abferguson/Camping-data-logger/CAD/exploded view.png

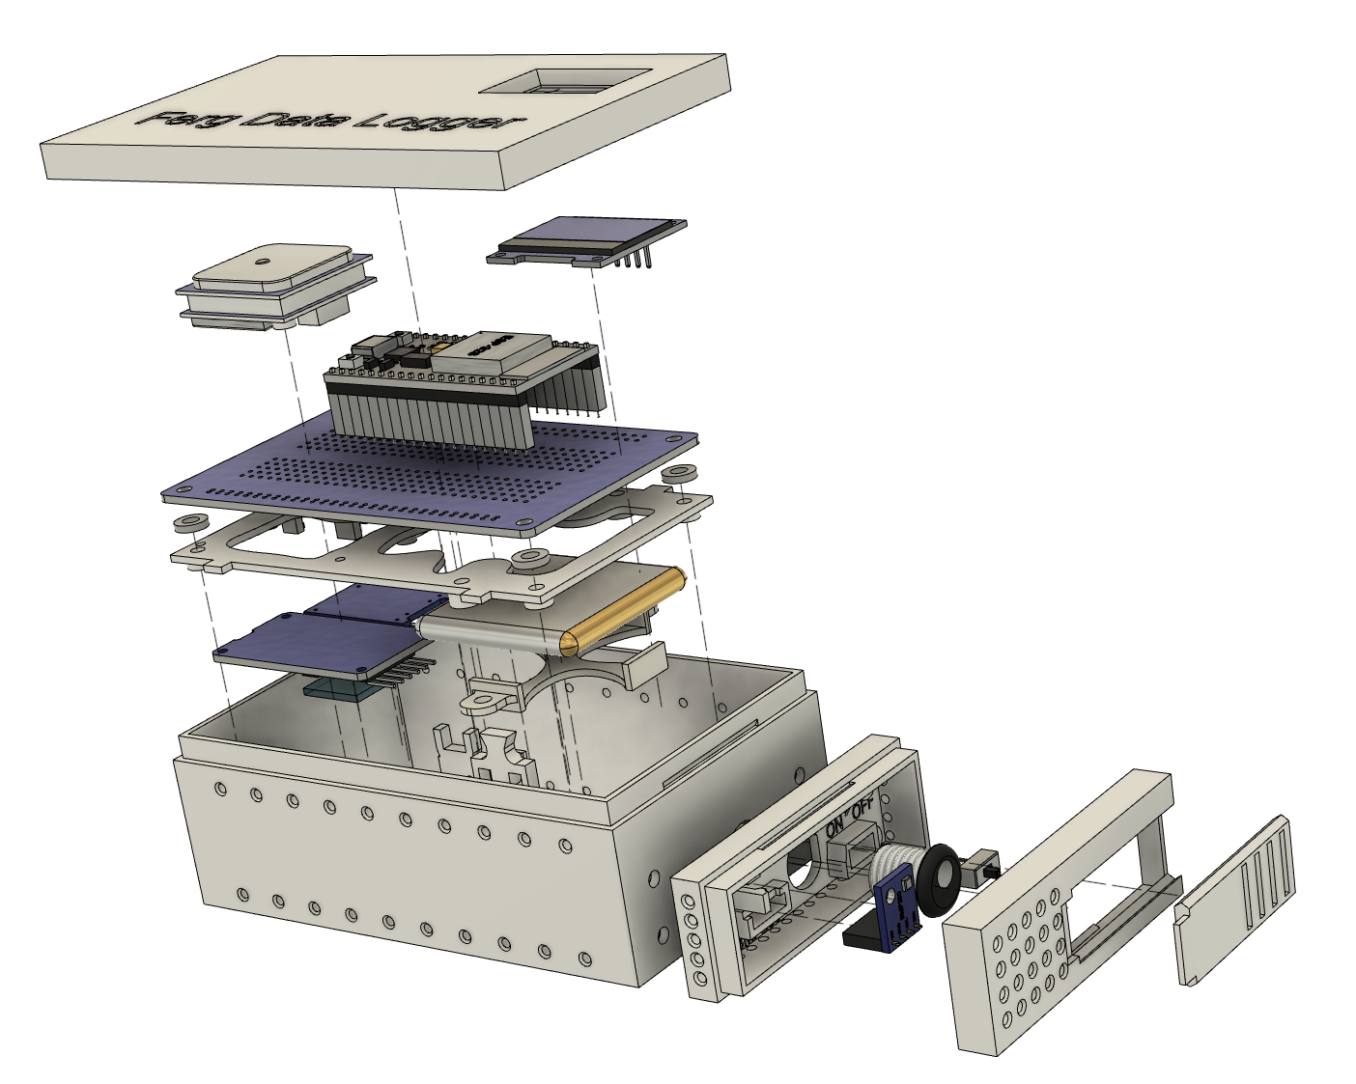
CAD/exploded view.png
