abferguson/Camping-data-logger/Circuit/data logger circuit.JPG

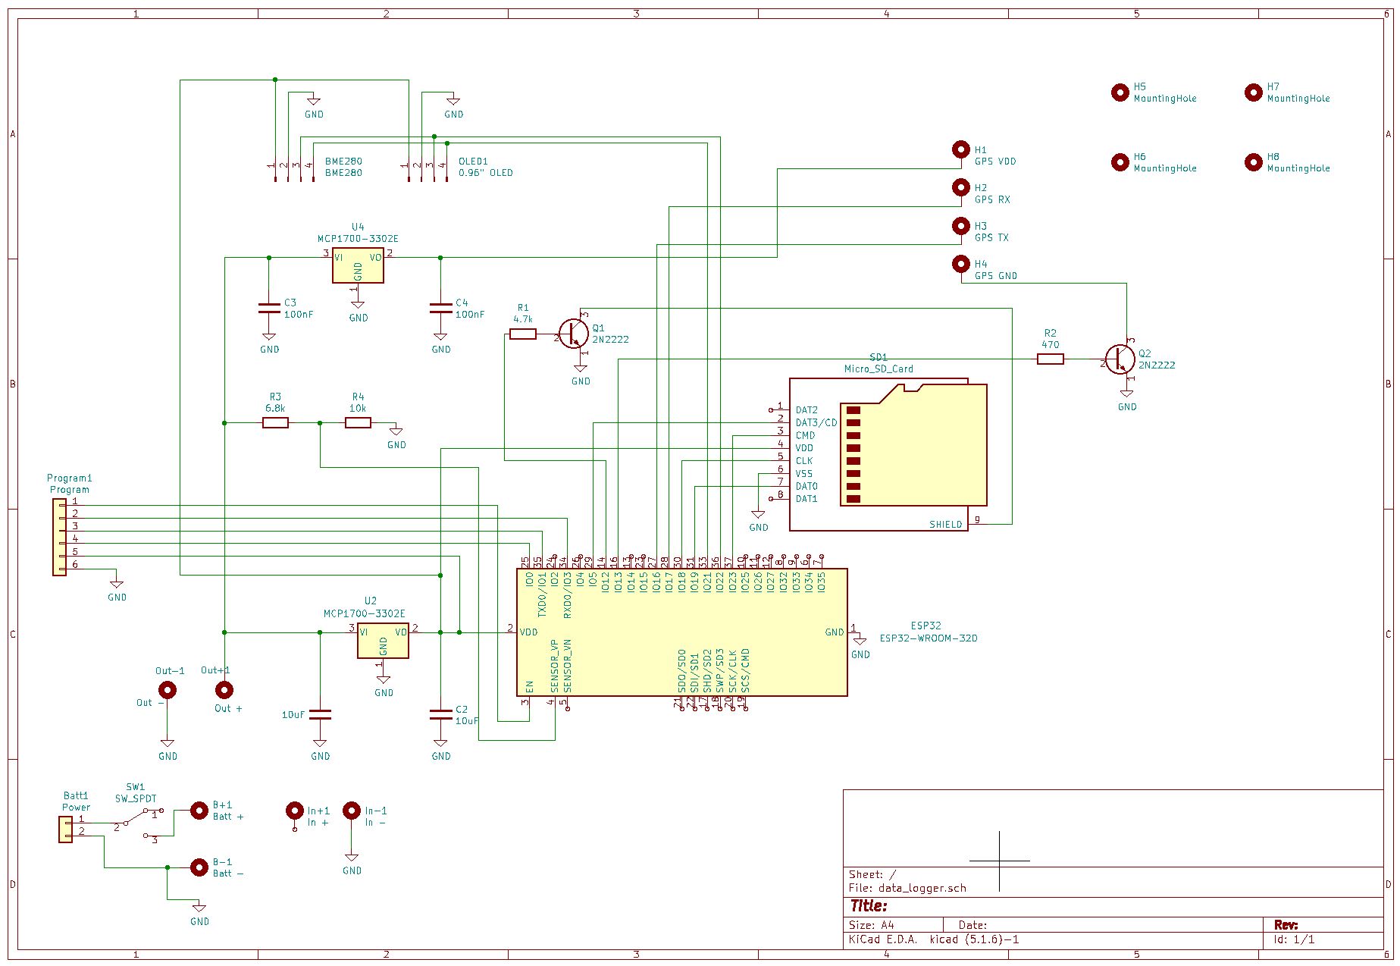
Circuit/data logger circuit.JPG
