abferguson/Camping-data-logger/Circuit/v11_circuit.JPG

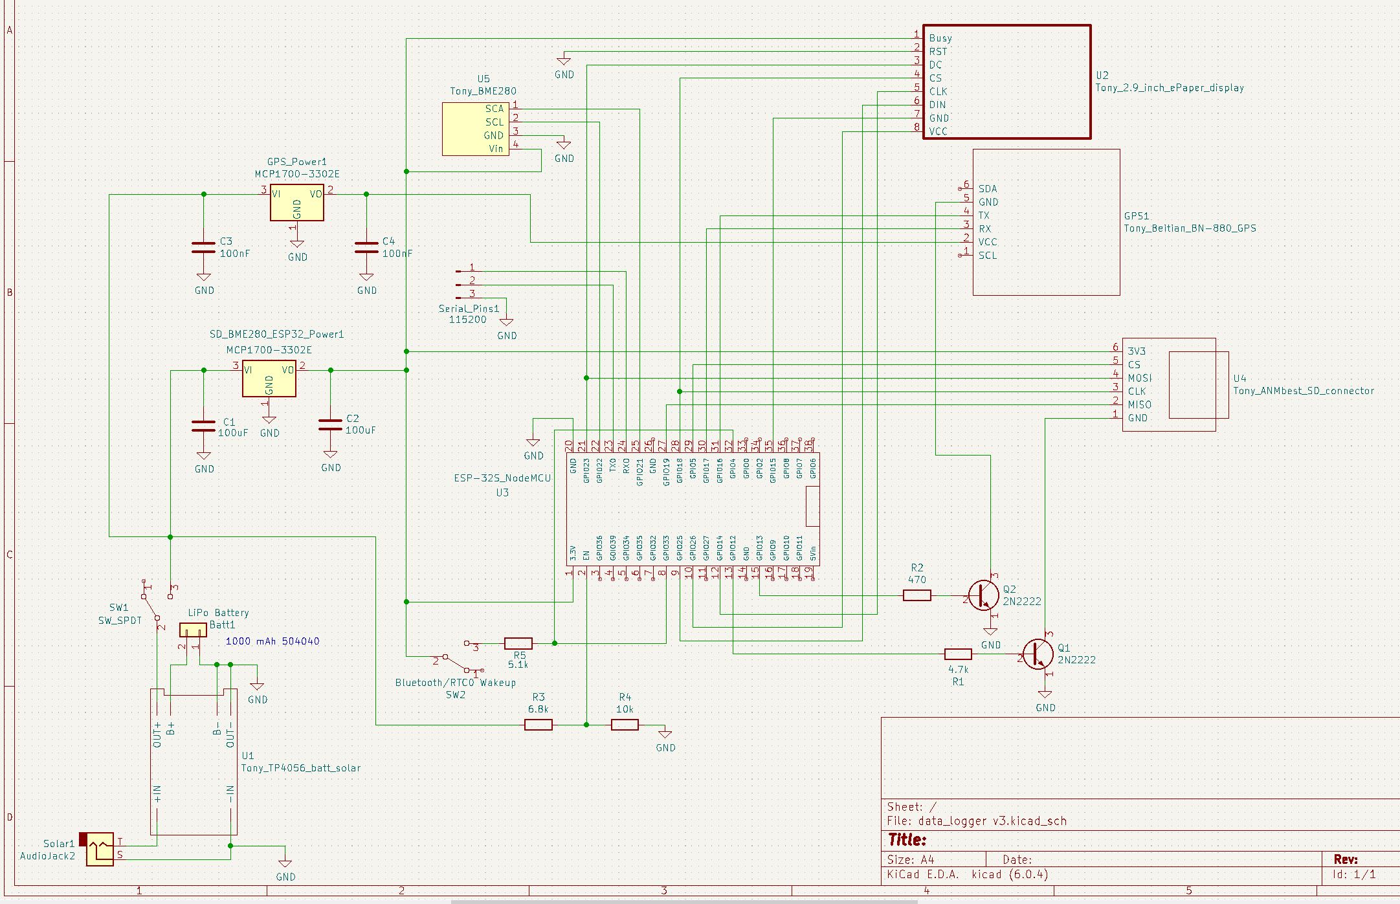
Circuit/v11_circuit.JPG
