abferguson/Camping-data-logger/Images/ABF_3092.jpg

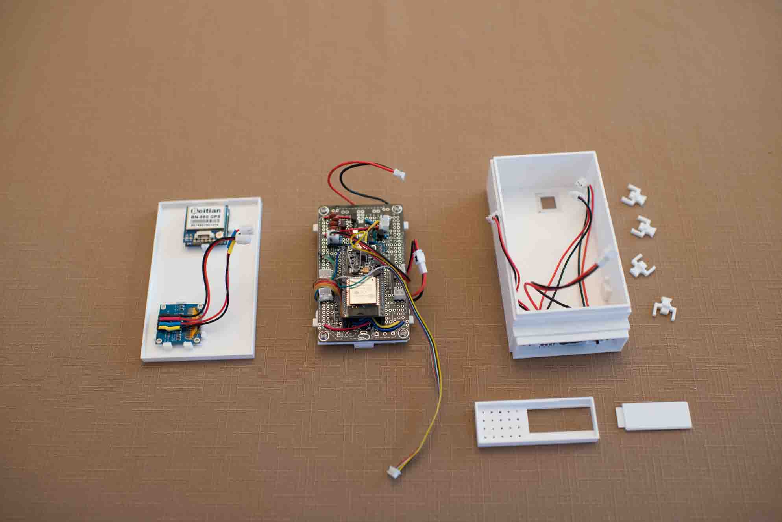
Images/ABF_3092.jpg
