abferguson/Camping-data-logger/Images/ABF_3096.jpg

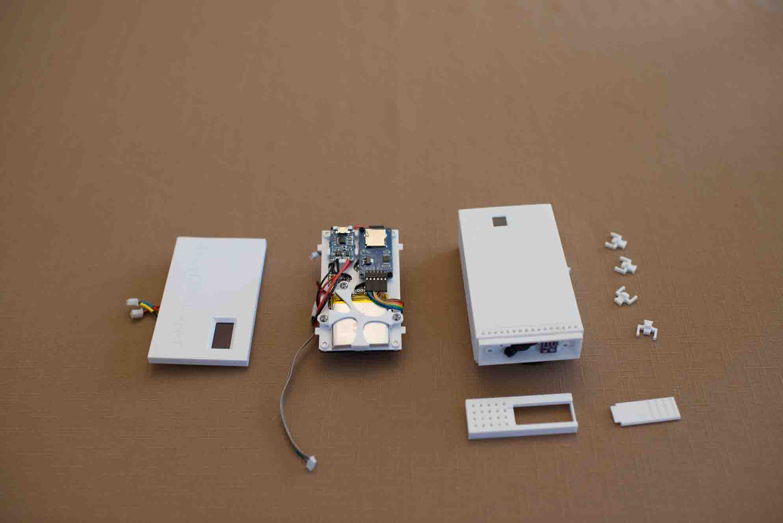
Images/ABF_3096.jpg
