abferguson/Camping-data-logger/Images/ABF_3097.jpg

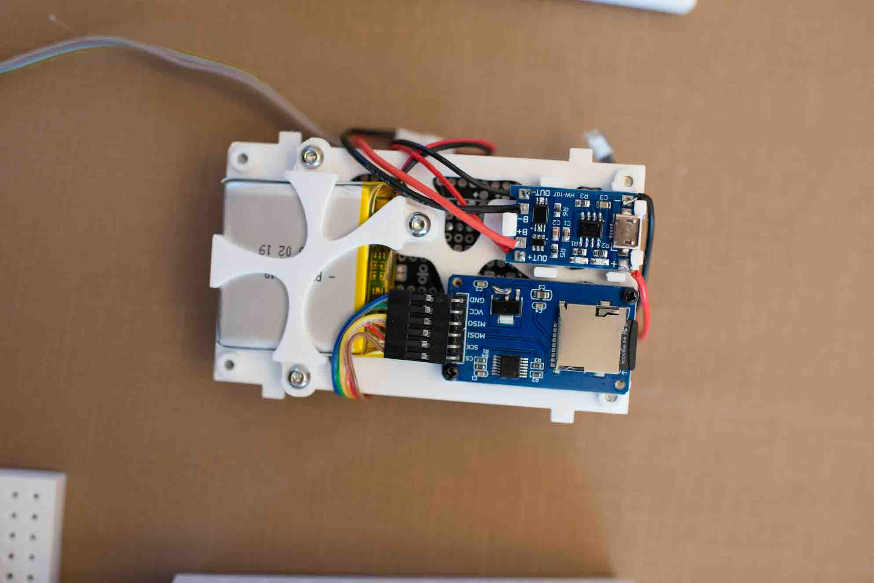
Images/ABF_3097.jpg
