abferguson/Camping-data-logger/Images/ABF_3098.jpg

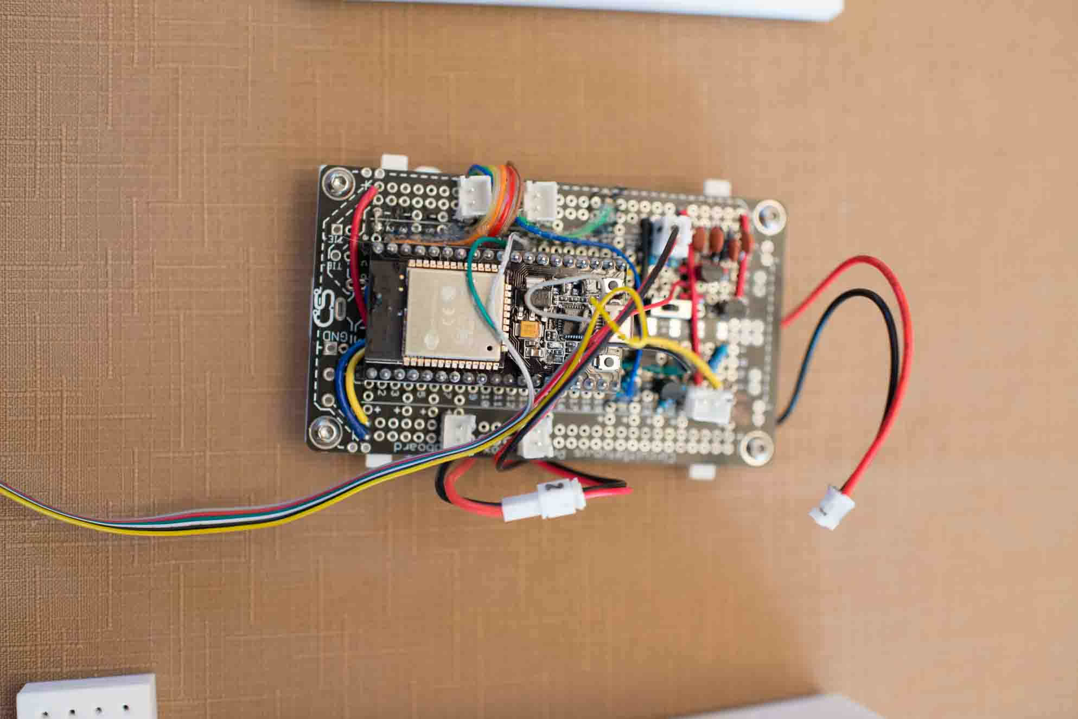
Images/ABF_3098.jpg
