abferguson/Camping-data-logger/Images/ABF_3099.jpg

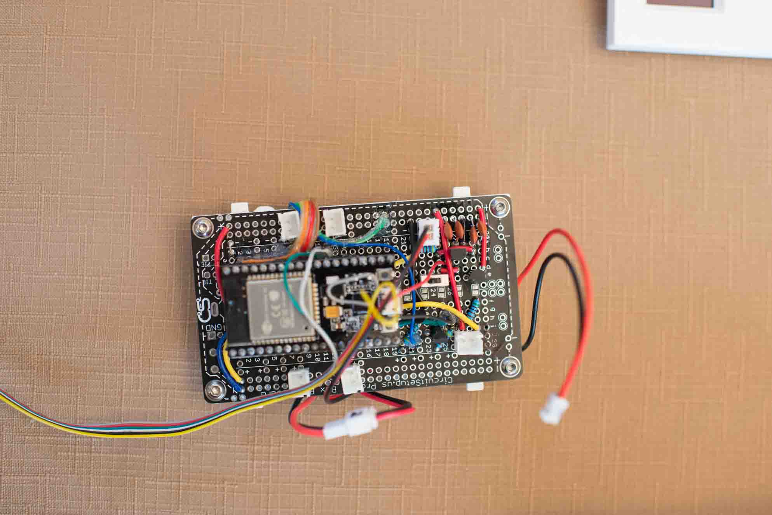
Images/ABF_3099.jpg
