abferguson/Camping-data-logger/Images/ABF_3101.jpg

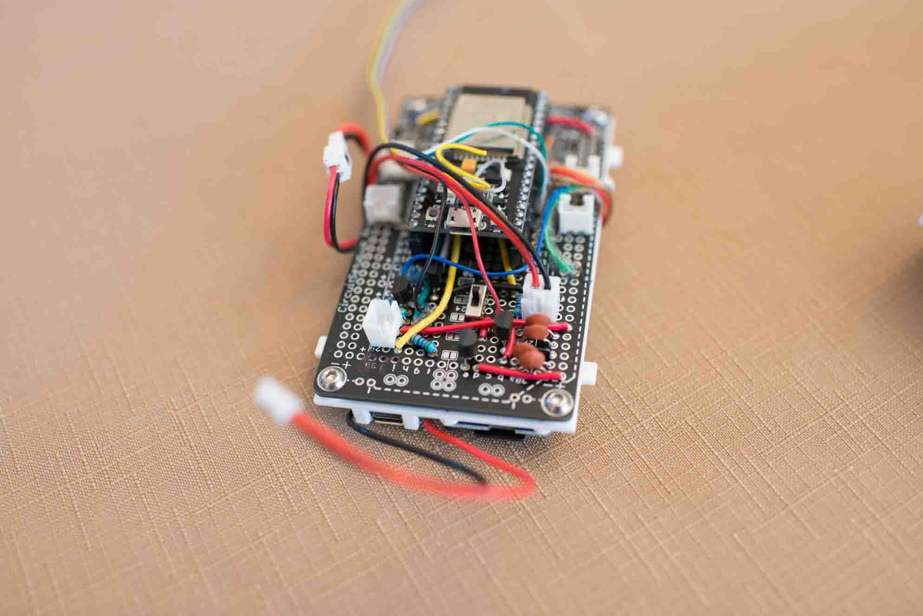
Images/ABF_3101.jpg
