abferguson/Camping-data-logger/Images/CAD render 1.png

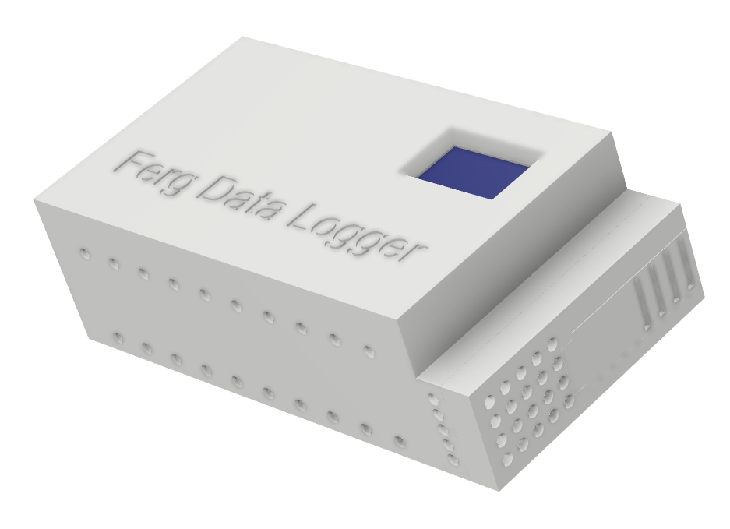
Images/CAD render 1.png
