abferguson/Camping-data-logger/Images/v11_cad_render.JPG

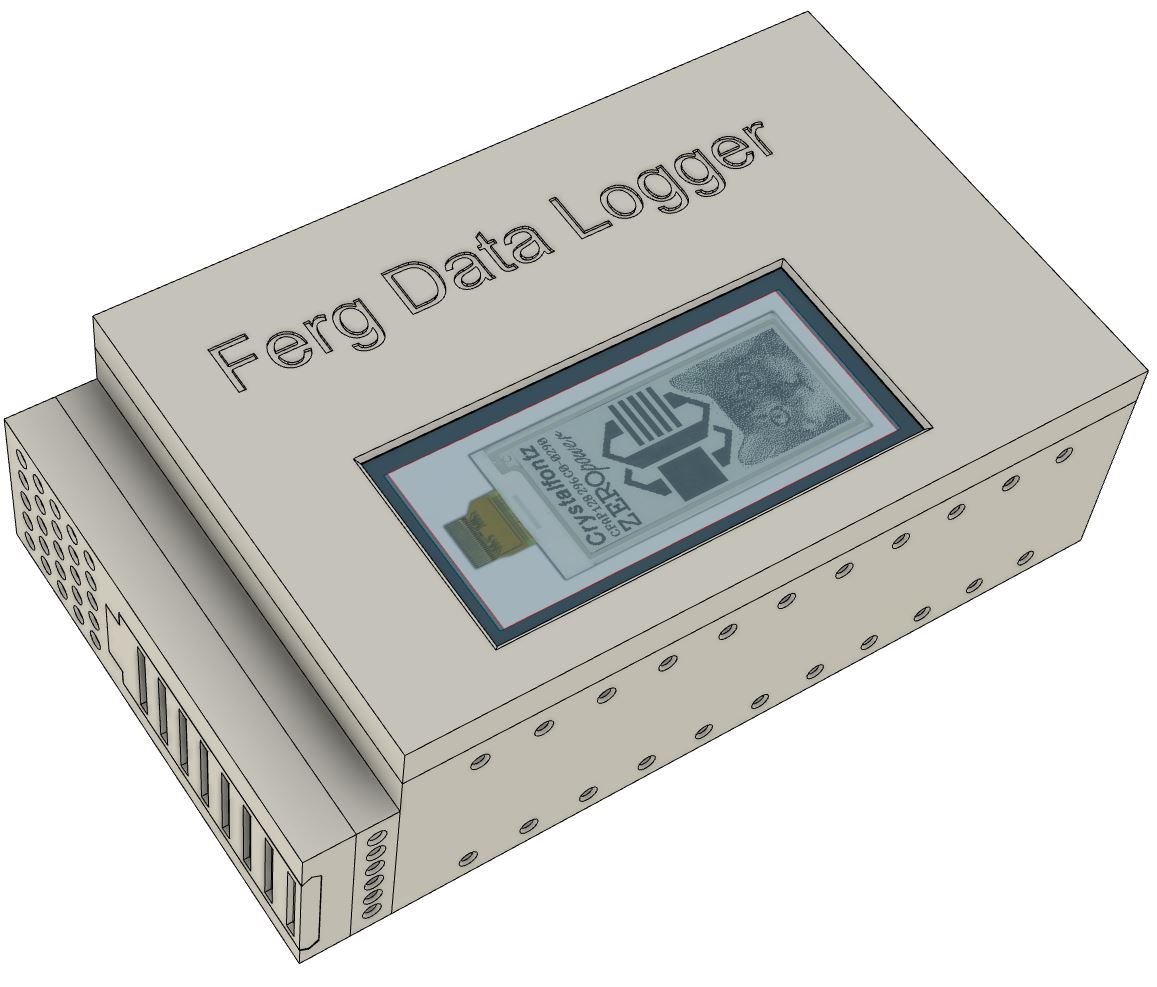
Images/v11_cad_render.JPG
