abferguson/Camping-data-logger/Circuit/epaper_data_logger.sch

## KiCad design Circuit/epaper_data_logger.sch (2022-04-28)

Schematic: epaper_data_logger.sch

Parts:
Batt1: LiPo Battery; JST_PH_B2B-PH-K_1x02_P2.00mm_Vertical
C1, C2: 100uF; C_Disc_D5.0mm_W2.5mm_P5.00mm
C3, C4: 100nF; C_Disc_D5.0mm_W2.5mm_P5.00mm
GPS1: Tony_Beitian_BN-880_GPS
GPS_Power1: MCP1700-3302E; TO-92_Inline
Q1, Q2: 2N2222; TO-92_Inline
R1: 4.7k; R_Axial_DIN0207_L6.3mm_D2.5mm_P7.62mm_Horizontal
R2: 470; R_Axial_DIN0207_L6.3mm_D2.5mm_P7.62mm_Horizontal
R3: 6.8k; R_Axial_DIN0207_L6.3mm_D2.5mm_P7.62mm_Horizontal
R4: 10k; R_Axial_DIN0207_L6.3mm_D2.5mm_P7.62mm_Horizontal
R5: 5.1k; R_Axial_DIN0207_L6.3mm_D2.5mm_P7.62mm_Horizontal
SD_BME280_ESP32_Power1: MCP1700-3302E; TO-92_Inline
SW1: SW_SPDT; Tony_slide_SPDT_switch
SW2: Bluetooth/RTC0 Wakeup; Tony_slide_SPDT_switch
Serial_Pins1: 115200; PinHeader_1x03_P2.54mm_Vertical
Solar1: AudioJack2; Jack_3.5mm_QingPu_WQP-PJ398SM_Vertical_CircularHoles
U1: Tony_TP4056_batt_solar
U2: Tony_2.9_inch_ePaper_display; Tony_Waveshare_2.9_ePaper_display
U3: ESP-32S_NodeMCU; Tony_ESP-32S_NodeMCU
U4: Tony_ANMbest_SD_connector; Tony_ANMbest_micro_SD
U5: Tony_BME280
