abferguson/Camping-data-logger/Circuit/v10data_logger.sch

## KiCad design Circuit/v10data_logger.sch (2022-04-28)

Schematic: v10data_logger.sch

Parts:
B+1: Batt +; Pin_D0.7mm_L6.5mm_W1.8mm_FlatFork
B-1: Batt -; Pin_D0.7mm_L6.5mm_W1.8mm_FlatFork
BME280: BME280; PinHeader_1x04_P2.54mm_Vertical
Batt1: Power; JST_PH_S2B-PH-K_1x02_P2.00mm_Horizontal
C1, C2: 10uF; C_1206_3216Metric
C3, C4: 100nF; C_1206_3216Metric
ESP32: ESP32-WROOM-32D; ESP32-WROOM-32
H1: GPS VDD; TestPoint_THTPad_D1.0mm_Drill0.5mm
H2: GPS RX; TestPoint_THTPad_1.0x1.0mm_Drill0.5mm
H3: GPS TX; TestPoint_THTPad_1.0x1.0mm_Drill0.5mm
H4: GPS GND; TestPoint_THTPad_1.0x1.0mm_Drill0.5mm
H5, H6, H7, H8: MountingHole; MountingHole_3.2mm_M3_DIN965_Pad
In+1: In +; Pin_D0.7mm_L6.5mm_W1.8mm_FlatFork
In-1: In -; Pin_D0.7mm_L6.5mm_W1.8mm_FlatFork
OLED1: 0.96\" OLED; PinHeader_1x04_P2.54mm_Vertical
Out+1: Out +; Pin_D0.7mm_L6.5mm_W1.8mm_FlatFork
Out-1: Out -; Pin_D0.7mm_L6.5mm_W1.8mm_FlatFork
Program1: Program; JST_XH_B6B-XH-A_1x06_P2.50mm_Vertical
Q1, Q2: 2N2222; SOT-23
R1: 4.7k; R_1206_3216Metric
R2: 470; R_1206_3216Metric
R3: 6.8k; R_1206_3216Metric
R4: 10k; R_1206_3216Metric
SD1: Micro_SD_Card; microSD_HC_Hirose_DM3AT-SF-PEJM5
SW1: SW_SPDT; PinHeader_1x03_P2.54mm_Vertical
U2, U4: MCP1700-3302E; SOT-23
